aindustriosa/micromouse_maze_design/poles_3d_design/A8_poste_0_pared.stl

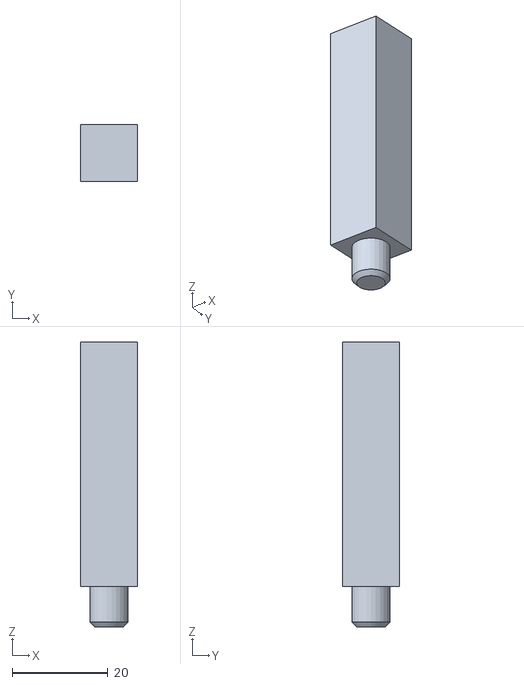
[picture p19: CAD file, 2019-07-25]
poles_3d_design/A8_poste_0_pared.stl
12.0 x 12.0 x 59.5
