aindustriosa/micromouse_maze_design/poles_3d_design/A8_poste_4_paredes.stl

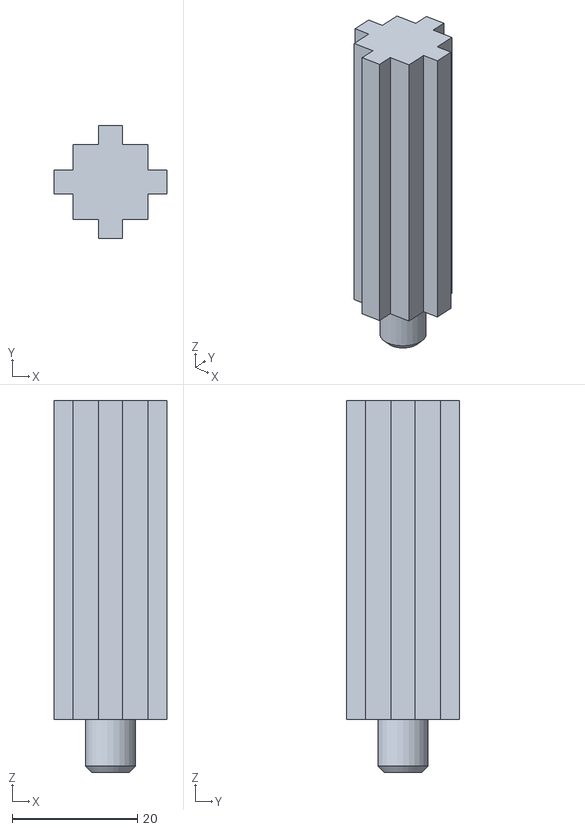
[picture p20: CAD file, 2019-06-29]
poles_3d_design/A8_poste_4_paredes.stl
18.0 x 18.0 x 59.5
