aindustriosa/micromouse_maze_design/poles_3d_design/A8_poste_3_paredes.stl

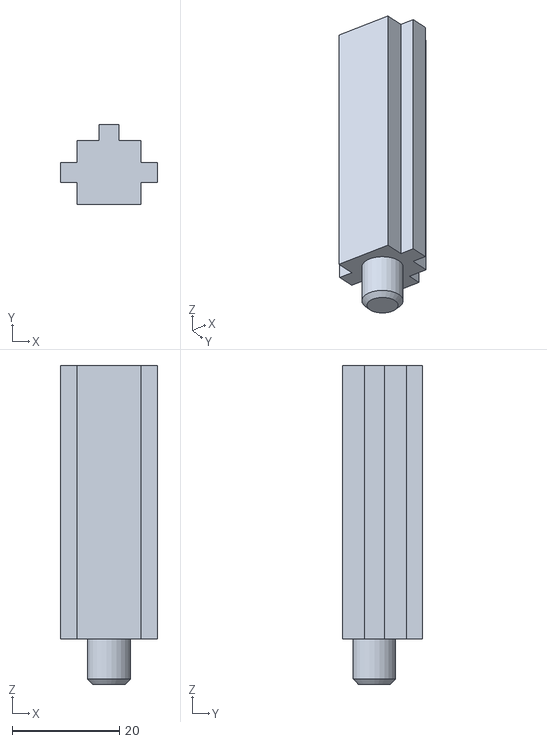
[picture p21: CAD file, 2019-06-29]
poles_3d_design/A8_poste_3_paredes.stl
18.0 x 15.0 x 59.5
